shimniok/Pokey/ff/I2C_master.c

#ifndef  F_CPU
#define F_CPU 16000000UL
#endif

#include <avr/io.h>
#include <util/twi.h>

#include "I2C_master.h"

#define F_SCL 100000UL // SCL frequency
#define Prescaler 1
#define TWBR_val ((((F_CPU / F_SCL) / Prescaler) - 16 ) / 2)

void I2C_init(void) {
	TWBR = TWBR_val;
}

uint8_t I2C_start(const uint8_t address, const uint8_t read) {
	// reset TWI control register
	TWCR = 0;
	// transmit START condition 
	TWCR = (1 << TWINT) | (1 << TWSTA) | (1 << TWEN);
	// wait for end of transmission
	while (!(TWCR & (1 << TWINT)))
		;

	// check if the start condition was successfully transmitted
	if ((TWSR & 0xF8) != TW_START) {
		return 1;
	}

	// load slave address into data register
	TWDR = (address << 1) | (read ? 1 : 0);
	// start transmission of address
	TWCR = (1 << TWINT) | (1 << TWEN);
	// wait for end of transmission
	while (!(TWCR & (1 << TWINT)))
		;

	// check if the device has acknowledged the READ / WRITE mode
	uint8_t twst = TW_STATUS & 0xF8;
	if ((twst != TW_MT_SLA_ACK) && (twst != TW_MR_SLA_ACK))
		return 1;

	return 0;
}

uint8_t I2C_write(const uint8_t data) {
	// load data into data register
	TWDR = data;
	// start transmission of data
	TWCR = (1 << TWINT) | (1 << TWEN);
	// wait for end of transmission
	while (!(TWCR & (1 << TWINT)))
		;

	if ((TWSR & 0xF8) != TW_MT_DATA_ACK) {
		return 1;
	}

	return 0;
}

uint8_t I2C_read(const uint8_t ack) {

	// start TWI module and acknowledge data after reception
	TWCR = (1 << TWINT) | (1 << TWEN) | ( ack ? (1 << TWEA) : 0 );
	// wait for end of transmission
	while (!(TWCR & (1 << TWINT)))
		;
	// return received data from TWDR
	return TWDR;
}

void I2C_stop(void) {
	// transmit STOP condition
	TWCR = (1 << TWINT) | (1 << TWEN) | (1 << TWSTO);
}
